Here-Be-Dragons/familamp/images/bottom.jpg

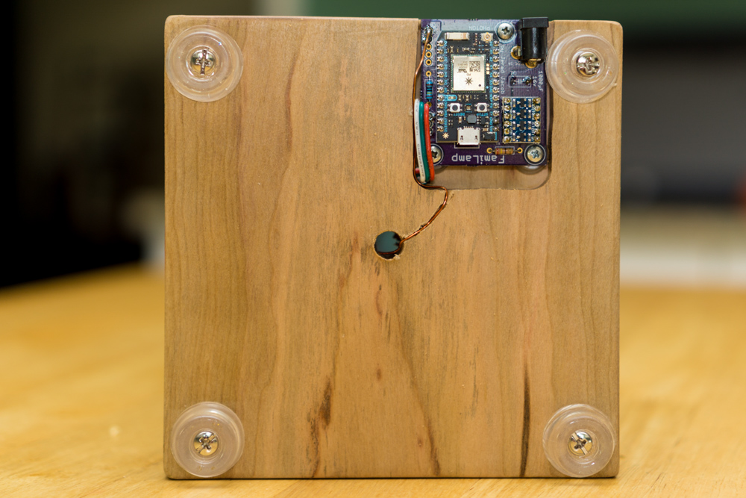
images/bottom.jpg
