Here-Be-Dragons/familamp/images/Lamp_example.jpg

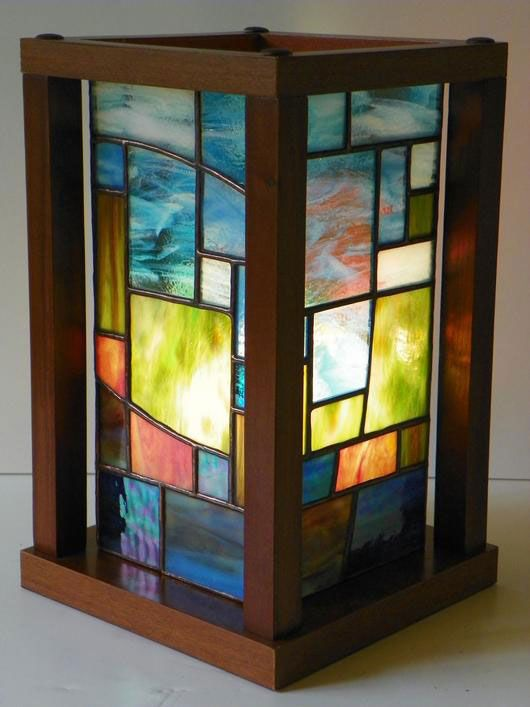
images/Lamp_example.jpg
