Here-Be-Dragons/familamp/images/OSH Park/2cfb63de5ff7d7a330a28cfda8a2cc61.png

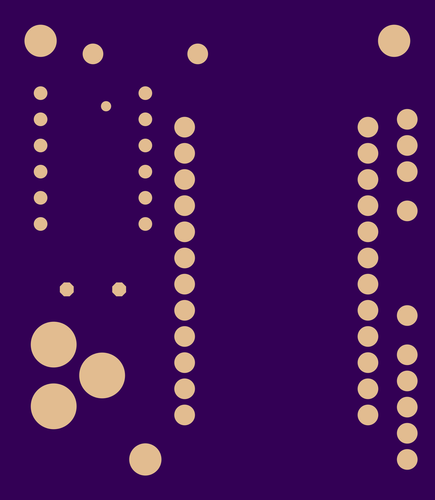
images/OSH Park/2cfb63de5ff7d7a330a28cfda8a2cc61.png
