Here-Be-Dragons/familamp/images/OSH Park/07cb042008991caee9ee7de78b667b51.png

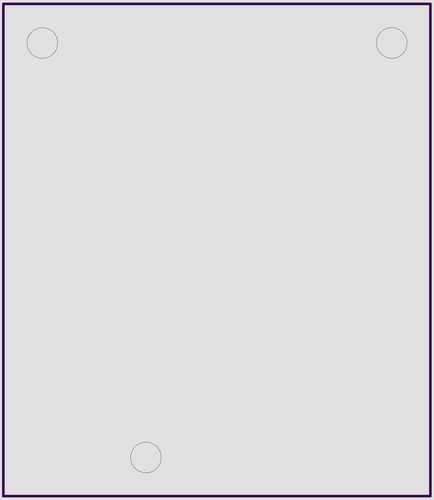
images/OSH Park/07cb042008991caee9ee7de78b667b51.png
