Here-Be-Dragons/familamp/images/OSH Park/104c008c561a3f2fd02f9e206726249a.png

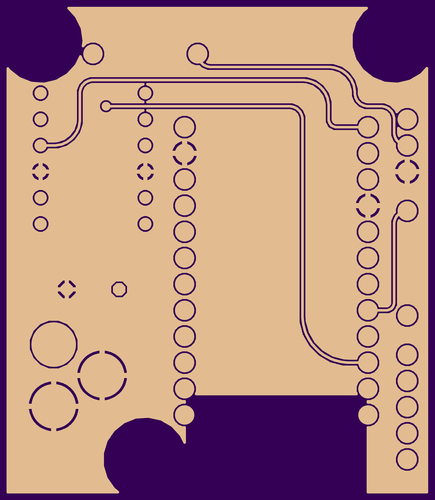
images/OSH Park/104c008c561a3f2fd02f9e206726249a.png
