Here-Be-Dragons/familamp/images/OSH Park/27975cea8cd203d67772c1c01c877c57.png

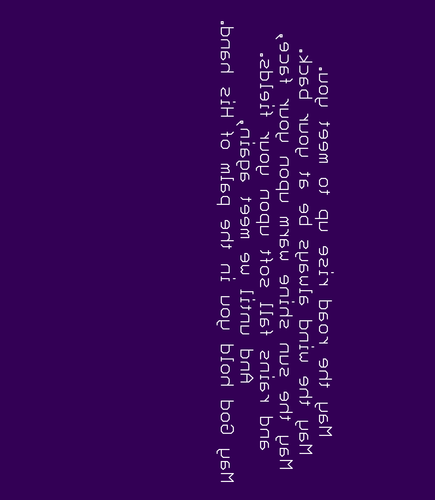
images/OSH Park/27975cea8cd203d67772c1c01c877c57.png
