Here-Be-Dragons/familamp/images/OSH Park/b69dff44d1d09abef398e9c6c776884b.png

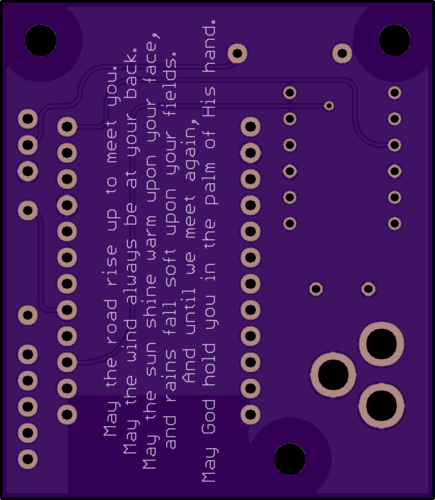
images/OSH Park/b69dff44d1d09abef398e9c6c776884b.png
