Here-Be-Dragons/familamp/images/SketchUp/familamp_3d.jpg

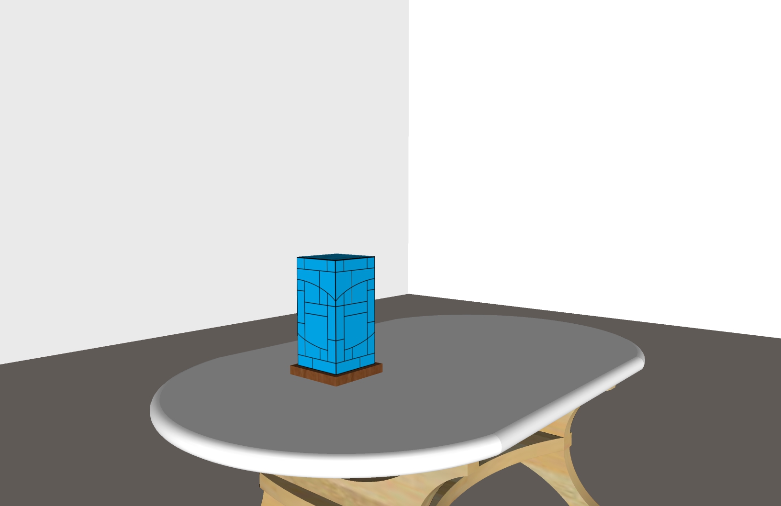
images/SketchUp/familamp_3d.jpg
